pruttelherrie/Ehx9-All/controller-firmware/include/Amiga4Ever6pt7b.h

const uint8_t amiga4ever6pt7bBitmaps[] PROGMEM = {
  0x00, 0xFF, 0xFF, 0xFF, 0x00, 0x0F, 0xF0, 0xF7, 0xF7, 0xF7, 0xF0, 0x7B,
  0x8F, 0x71, 0xEE, 0x7F, 0xFF, 0xFE, 0xF7, 0x3F, 0xFF, 0xFF, 0x7B, 0x8F,
  0x71, 0xEE, 0x00, 0x1E, 0x0F, 0xF3, 0xFF, 0xC0, 0xF0, 0x0F, 0xC3, 0xF0,
  0x0F, 0xFF, 0x3F, 0xC1, 0xE0, 0x38, 0xE7, 0x1F, 0x6E, 0x73, 0x81, 0x6E,
  0x39, 0xCE, 0xDF, 0x1C, 0xE3, 0x80, 0x1F, 0x00, 0xF8, 0x0E, 0xF0, 0x77,
  0x83, 0xB0, 0x1E, 0x70, 0xF3, 0x9D, 0xF8, 0xE3, 0xE1, 0xFF, 0xCF, 0xFE,
  0x7B, 0xDF, 0xCE, 0x00, 0x1C, 0x77, 0xB8, 0xE3, 0x8E, 0x38, 0x78, 0x71,
  0xC0, 0xE3, 0x87, 0x87, 0x1C, 0x71, 0xC7, 0x7B, 0x8E, 0x00, 0x79, 0xE7,
  0x9E, 0x1F, 0x8F, 0xFF, 0xFF, 0xF1, 0xF8, 0x79, 0xE7, 0x9E, 0x1E, 0x07,
  0x81, 0xE3, 0xFF, 0xFF, 0xC7, 0x81, 0xE0, 0x7B, 0xDF, 0xC0, 0xFF, 0xFF,
  0xF0, 0xFF, 0xF0, 0x00, 0x70, 0x07, 0x01, 0xE0, 0x38, 0x03, 0x80, 0xF0,
  0x1C, 0x01, 0xC0, 0x78, 0x0E, 0x00, 0xE0, 0x00, 0x3F, 0x0F, 0xCF, 0x3F,
  0xDF, 0xF7, 0xFF, 0xFF, 0xBF, 0xEF, 0xF3, 0xCF, 0xC3, 0xF0, 0x1E, 0x7C,
  0xFF, 0xFF, 0xE3, 0xC7, 0x8F, 0x1E, 0x3C, 0x78, 0x3F, 0x0F, 0xCF, 0x3F,
  0xCF, 0x03, 0xC1, 0xC1, 0xE0, 0x78, 0x38, 0x3F, 0xFF, 0xFC, 0x3F, 0x0F,
  0xCF, 0x3F, 0xCF, 0x03, 0xC7, 0xC1, 0xF0, 0x0F, 0xF3, 0xFC, 0xF3, 0xF0,
  0x0F, 0x81, 0xF0, 0x7E, 0x3D, 0xC7, 0xB9, 0xC7, 0x3F, 0xFF, 0xFF, 0x03,
  0x80, 0x70, 0x0E, 0x00, 0xFF, 0xFF, 0xFF, 0x03, 0xFC, 0xFF, 0x00, 0xF0,
  0x3C, 0x0F, 0xF3, 0xFC, 0xF3, 0xF0, 0x1F, 0x07, 0xC3, 0x83, 0xE0, 0xF0,
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
  {   418,  10,  11,  12,    1,  -10 },   // 0x46 'F'
  {   432,  10,  11,  12,    1,  -10 },   // 0x47 'G'
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

const GFXfont amiga4ever6pt7b PROGMEM = {
  (uint8_t  *)amiga4ever6pt7bBitmaps,
  (GFXglyph *)amiga4ever6pt7bGlyphs,
  0x20, 0x7E, 12 };

// Approx. 1783 bytes
