pruttelherrie/Ehx9-All/controller-firmware/include/Amiga4Ever8pt7b.h

const uint8_t amiga4ever8pt7bBitmaps[] PROGMEM = {
  0x00, 0xFF, 0xFF, 0xFF, 0xFF, 0x00, 0x00, 0xFF, 0xF3, 0xFC, 0xFF, 0x3F,
  0xCF, 0x3C, 0xF0, 0xF3, 0xC3, 0xCF, 0x0F, 0x3C, 0xFF, 0xFF, 0xFF, 0xF3,
  0xCF, 0x0F, 0x3C, 0xFF, 0xFF, 0xFF, 0xF3, 0xCF, 0x0F, 0x3C, 0x3C, 0xF0,
  0xF3, 0xC0, 0x0F, 0x00, 0xF0, 0x3F, 0xF3, 0xFF, 0xF0, 0x0F, 0x00, 0x3F,
  0xC3, 0xFC, 0x00, 0xF0, 0x0F, 0xFF, 0xCF, 0xFC, 0x0F, 0x00, 0xF0, 0x3C,
  0x3C, 0xF0, 0xFC, 0xCF, 0x33, 0x3C, 0xF3, 0xC3, 0xCF, 0x00, 0xF3, 0xC3,
  0xCF, 0x3C, 0xCC, 0xF3, 0x3F, 0x0F, 0x3C, 0x3C, 0x0F, 0xC0, 0x0F, 0xC0,
  0x3C, 0xF0, 0x3C, 0xF0, 0x3C, 0xC0, 0x3C, 0xC0, 0x3F, 0x3C, 0x3F, 0x3C,
  0xF3, 0xF0, 0xF3, 0xF0, 0xF0, 0xFC, 0xF0, 0xFC, 0x3F, 0xFF, 0x3F, 0xFF,
  0x3C, 0xF3, 0xCF, 0xF3, 0xC0, 0x0F, 0x0F, 0x3C, 0x3C, 0xF0, 0xF0, 0xF0,
  0xF0, 0xF0, 0xF0, 0x3C, 0x3C, 0x0F, 0x0F, 0xF0, 0xF0, 0x3C, 0x3C, 0x0F,
  0x0F, 0x0F, 0x0F, 0x0F, 0x0F, 0x3C, 0x3C, 0xF0, 0xF0, 0x3C, 0x3C, 0x3C,
  0x3C, 0x0F, 0xF0, 0x0F, 0xF0, 0xFF, 0xFF, 0xFF, 0xFF, 0x0F, 0xF0, 0x0F,
  0xF0, 0x3C, 0x3C, 0x3C, 0x3C, 0x0F, 0x00, 0xF0, 0x0F, 0x00, 0xF0, 0xFF,
  0xFF, 0xFF, 0x0F, 0x00, 0xF0, 0x0F, 0x00, 0xF0, 0x3C, 0xF3, 0xCF, 0xF3,
  0xC0, 0xFF, 0xFF, 0xFF, 0xFF, 0xFF, 0x00, 0x0F, 0x00, 0x0F, 0x00, 0x3C,
  0x00, 0x3C, 0x00, 0xF0, 0x00, 0xF0, 0x03, 0xC0, 0x03, 0xC0, 0x0F, 0x00,
  0x0F, 0x00, 0x3C, 0x00, 0x3C, 0x00, 0xF0, 0x00, 0xF0, 0x00, 0x3F, 0xC3,
  0xFC, 0xF0, 0xFF, 0x0F, 0xF3, 0xFF, 0x3F, 0xFF, 0xFF, 0xFF, 0xFC, 0xFF,
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
  {   628,  12,  14,  16,    2,  -13 },   // 0x46 'F'
  {   649,  12,  14,  16,    2,  -13 },   // 0x47 'G'
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

const GFXfont amiga4ever8pt7b PROGMEM = {
  (uint8_t  *)amiga4ever8pt7bBitmaps,
  (GFXglyph *)amiga4ever8pt7bGlyphs,
  0x20, 0x7E, 16 };

// Approx. 2344 bytes
