pruttelherrie/Ehx9-All/controller-firmware/include/LiberationSans8pt7b.h

const uint8_t LiberationSans_Regular8pt7bBitmaps[] PROGMEM = {
  0x00, 0xFF, 0x60, 0x99, 0x90, 0x11, 0x08, 0x84, 0x5F, 0xF2, 0x21, 0x10,
  0x89, 0xFF, 0x44, 0x22, 0x11, 0x00, 0x10, 0xFA, 0x4C, 0x89, 0x0A, 0x0E,
  0x0A, 0x12, 0x26, 0x4B, 0xE1, 0x00, 0x70, 0x48, 0x88, 0x88, 0x88, 0x90,
  0x8A, 0x07, 0x4E, 0x05, 0x10, 0x91, 0x11, 0x11, 0x11, 0x20, 0xE0, 0x1C,
  0x11, 0x08, 0x84, 0x82, 0x82, 0x8A, 0x25, 0x12, 0x86, 0x43, 0x1E, 0x60,
  0xE0, 0x12, 0x44, 0x88, 0x88, 0x88, 0x84, 0x42, 0x10, 0x84, 0x22, 0x11,
  0x11, 0x11, 0x12, 0x24, 0x80, 0x21, 0x3E, 0x45, 0x44, 0x10, 0x20, 0x47,
  0xF1, 0x02, 0x04, 0x00, 0x56, 0xE0, 0xC0, 0x11, 0x22, 0x22, 0x44, 0x44,
  0x88, 0x38, 0x8A, 0x0C, 0x18, 0x30, 0x60, 0xC1, 0x82, 0x88, 0xE0, 0x30,
  0xA2, 0x40, 0x81, 0x02, 0x04, 0x08, 0x10, 0x23, 0xF8, 0x79, 0x08, 0x08,
  0x10, 0x20, 0x82, 0x18, 0x41, 0x03, 0xF8, 0x79, 0x08, 0x08, 0x10, 0x43,
  0x01, 0x01, 0x03, 0x09, 0xE0, 0x04, 0x0C, 0x14, 0x24, 0x24, 0x44, 0x84,
  0xFF, 0x04, 0x04, 0x04, 0xFF, 0x02, 0x04, 0x0B, 0x98, 0x80, 0x81, 0x03,
  0x09, 0xE0, 0x3C, 0x86, 0x04, 0x0B, 0x98, 0xA0, 0xC1, 0x82, 0x88, 0xE0,
  0xFE, 0x04, 0x10, 0x40, 0x82, 0x04, 0x08, 0x20, 0x40, 0x80, 0x38, 0x8A,
  0x0C, 0x14, 0x47, 0x11, 0x41, 0x82, 0x88, 0xE0, 0x38, 0x8A, 0x0C, 0x18,
  0x28, 0xCE, 0x81, 0x03, 0x09, 0xE0, 0xC1, 0x80, 0x50, 0x01, 0x58, 0x02,
  0x39, 0x84, 0x06, 0x03, 0x80, 0x80, 0xFE, 0x00, 0x00, 0x0F, 0xE0, 0x80,
  0xE0, 0x30, 0x10, 0xCE, 0x20, 0x00, 0x38, 0x8A, 0x08, 0x10, 0x20, 0x82,
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
  {   338,  10,  11,  12,    1,  -10 },   // 0x47 'G'
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

const GFXfont LiberationSans_Regular8pt7b PROGMEM = {
  (uint8_t  *)LiberationSans_Regular8pt7bBitmaps,
  (GFXglyph *)LiberationSans_Regular8pt7bGlyphs,
  0x20, 0x7E, 18 };

// Approx. 1539 bytes
