pruttelherrie/Ehx9-All/controller-firmware/include/LiberationSansBold7pt7b.h

const uint8_t LiberationSans_Bold7pt7bBitmaps[] PROGMEM = {
  0x00, 0xFF, 0xFC, 0xF0, 0xDE, 0xF7, 0xB0, 0x12, 0x12, 0x12, 0x7F, 0x24,
  0x24, 0xFE, 0x48, 0x48, 0x48, 0x11, 0xEF, 0xFB, 0xE1, 0xE0, 0xF3, 0xFD,
  0xE1, 0x00, 0x61, 0x24, 0x89, 0x22, 0x50, 0x95, 0x9A, 0x90, 0xA4, 0x49,
  0x12, 0x48, 0x60, 0x38, 0x7C, 0x6C, 0x78, 0x63, 0xF3, 0xDE, 0xCC, 0xFF,
  0x73, 0xFF, 0x36, 0x6C, 0xCC, 0xCC, 0xCC, 0xC6, 0x63, 0xC6, 0x63, 0x33,
  0x33, 0x33, 0x36, 0x6C, 0x25, 0x7E, 0xA5, 0x00, 0x18, 0x18, 0x18, 0xFF,
  0xFF, 0x18, 0x18, 0x18, 0xF7, 0xFC, 0xF0, 0x33, 0x32, 0x66, 0x64, 0xCC,
  0xC0, 0x79, 0xEC, 0xF3, 0xCF, 0x3C, 0xF3, 0x79, 0xE0, 0x73, 0xCB, 0x0C,
  0x30, 0xC3, 0x0C, 0xFF, 0xF0, 0x7B, 0xFC, 0xC3, 0x1C, 0xE7, 0x18, 0xFF,
  0xF0, 0x7B, 0xFC, 0xC3, 0x38, 0xE0, 0xF3, 0xFD, 0xE0, 0x1C, 0x38, 0xF1,
  0x64, 0xD9, 0xBF, 0xFF, 0x0C, 0x18, 0xFF, 0xFC, 0x3E, 0xFC, 0x30, 0xF3,
  0xFD, 0xE0, 0x39, 0xFC, 0xF0, 0xFB, 0xFC, 0xF3, 0x7D, 0xE0, 0xFF, 0xF0,
  0xC6, 0x18, 0xC3, 0x18, 0x61, 0x80, 0x7B, 0xFC, 0xF3, 0x79, 0xEC, 0xF3,
  0xFD, 0xE0, 0x7B, 0xEC, 0xF3, 0xFD, 0xF0, 0xF3, 0xF9, 0xC0, 0xF0, 0x0F,
  0xF0, 0x0F, 0x70, 0x04, 0xFF, 0xB8, 0xE3, 0xE3, 0xC1, 0xFF, 0xF0, 0x3F,
  0xFC, 0x83, 0xC7, 0xC7, 0x1D, 0xFF, 0x20, 0x3D, 0xFF, 0x18, 0x30, 0xC3,
  0x0C, 0x00, 0x30, 0x60, 0x0F, 0x83, 0x06, 0x60, 0x24, 0xE9, 0x89, 0x99,
  0x11, 0x91, 0x19, 0x32, 0x8D, 0xC4, 0x00, 0x60, 0xC1, 0xF8, 0x1C, 0x0E,
  0x0D, 0x86, 0xC3, 0x63, 0x19, 0xFC, 0xFE, 0xE1, 0xE0, 0xC0, 0xFE, 0xFF,
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
  {   265,   7,  10,   9,    1,   -9 },   // 0x46 'F'
  {   274,   9,  10,  11,    1,   -9 },   // 0x47 'G'
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

const GFXfont LiberationSans_Bold7pt7b PROGMEM = {
  (uint8_t  *)LiberationSans_Bold7pt7bBitmaps,
  (GFXglyph *)LiberationSans_Bold7pt7bGlyphs,
  0x20, 0x7E, 16 };

// Approx. 1410 bytes
