pruttelherrie/Ehx9-All/controller-firmware/include/lovecraft24pt7b.h

const uint8_t Love_Craft_Italic24pt7bBitmaps[] PROGMEM = {
  0x00, 0x00, 0x03, 0xFF, 0x80, 0x00, 0x00, 0x00, 0xFF, 0xFF, 0x80, 0x00,
  0x00, 0x3F, 0xFF, 0xFF, 0x00, 0x00, 0x03, 0xFF, 0xFF, 0xFE, 0x00, 0x00,
  0x7F, 0xFC, 0x7F, 0xF8, 0x00, 0x0F, 0xFF, 0x81, 0xFF, 0xE0, 0x00, 0xFF,
  0xF8, 0x0F, 0xFF, 0x00, 0x0F, 0xFF, 0x80, 0x3F, 0xFC, 0x00, 0xFF, 0xF8,
  0x01, 0xFF, 0xE0, 0x0F, 0xFF, 0xC0, 0x0F, 0xFF, 0x80, 0xFF, 0xFC, 0x00,
  0x7F, 0xFC, 0x07, 0xFF, 0xE0, 0x03, 0xFF, 0xE0, 0x7F, 0xFE, 0x00, 0x1F,
  0xFF, 0x07, 0xFF, 0xF0, 0x00, 0xFF, 0xF8, 0x3F, 0xFF, 0x00, 0x07, 0xFF,
  0xE3, 0xFF, 0xF8, 0x00, 0x3F, 0xFF, 0x1F, 0xFF, 0xC0, 0x01, 0xFF, 0xF8,
  0xFF, 0xFC, 0x00, 0x1F, 0xFF, 0x87, 0xFF, 0xE0, 0x00, 0xFF, 0xFC, 0x7F,
  0xFF, 0x00, 0x07, 0xFF, 0xE3, 0xFF, 0xF0, 0x00, 0x3F, 0xFF, 0x1F, 0xFF,
  0x80, 0x03, 0xFF, 0xF0, 0xFF, 0xFC, 0x00, 0x1F, 0xFF, 0x87, 0xFF, 0xE0,
  0x01, 0xFF, 0xFC, 0x3F, 0xFF, 0x00, 0x0F, 0xFF, 0xC1, 0xFF, 0xF8, 0x00,
  0x7F, 0xFC, 0x0F, 0xFF, 0xC0, 0x07, 0xFF, 0xE0, 0x3F, 0xFE, 0x00, 0x3F,
  0xFE, 0x01, 0xFF, 0xF0, 0x03, 0xFF, 0xE0, 0x0F, 0xFF, 0x80, 0x3F, 0xFE,
  0x00, 0x3F, 0xFC, 0x01, 0xFF, 0xF0, 0x01, 0xFF, 0xE0, 0x1F, 0xFE, 0x00,
  0x07, 0xFF, 0x81, 0xFF, 0xE0, 0x00, 0x1F, 0xFE, 0x3F, 0xFE, 0x00, 0x00,
  0x7F, 0xFF, 0xFF, 0xE0, 0x00, 0x00, 0xFF, 0xFF, 0xFC, 0x00, 0x00, 0x01,
  0xFF, 0xFF, 0x00, 0x00, 0x00, 0x01, 0xFF, 0xC0, 0x00, 0x00, 0x00, 0x00,
  0x03, 0x80, 0x00, 0x07, 0xC0, 0x00, 0x3F, 0xE0, 0x00, 0xFF, 0xF0, 0x07,
  0xFF, 0xF8, 0x1F, 0xFF, 0xF8, 0x0F, 0xFF, 0xFC, 0x01, 0xFF, 0xFE, 0x00,
  0x3F, 0xFF, 0x00, 0x0F, 0xFF, 0x80, 0x0F, 0xFF, 0x80, 0x07, 0xFF, 0xC0,
  0x03, 0xFF, 0xE0, 0x01, 0xFF, 0xF0, 0x00, 0xFF, 0xF8, 0x00, 0xFF, 0xF8,
  0x00, 0x7F, 0xFC, 0x00, 0x3F, 0xFE, 0x00, 0x1F, 0xFF, 0x00, 0x1F, 0xFF,
  0x80, 0x0F, 0xFF, 0x80, 0x07, 0xFF, 0xC0, 0x03, 0xFF, 0xE0, 0x01, 0xFF,
  0xF0, 0x01, 0xFF, 0xF8, 0x00, 0xFF, 0xF8, 0x00, 0x7F, 0xFC, 0x00, 0x3F,
  0xFE, 0x00, 0x1F, 0xFF, 0x00, 0x1F, 0xFF, 0x80, 0x0F, 0xFF, 0x80, 0x07,
  0xFF, 0xC0, 0x03, 0xFF, 0xE0, 0x03, 0xFF, 0xF0, 0x03, 0xFF, 0xF8, 0x07,
  0xFF, 0xFE, 0x0F, 0xFF, 0xFF, 0xE7, 0xFF, 0xFF, 0xE0, 0x00, 0x00, 0x0F,
  0xFF, 0xC0, 0x00, 0x00, 0x1F, 0xFF, 0xFF, 0xC0, 0x00, 0x0F, 0xFF, 0xFF,
  0xFF, 0x00, 0x03, 0xFF, 0xFF, 0xFF, 0xF8, 0x00, 0xFF, 0xF8, 0x1F, 0xFF,
  0xC0, 0x1F, 0xFE, 0x00, 0x7F, 0xFE, 0x03, 0xFF, 0xC0, 0x03, 0xFF, 0xE0,
  0x3F, 0xF8, 0x00, 0x3F, 0xFF, 0x07, 0xFF, 0x80, 0x01, 0xFF, 0xF0, 0x7F,
  0xF8, 0x00, 0x1F, 0xFF, 0x03, 0xFF, 0x80, 0x01, 0xFF, 0xF0, 0x3F, 0xFF,
  0x80, 0x3F, 0xFF, 0x01, 0xFF, 0xF8, 0x03, 0xFF, 0xF0, 0x0F, 0xFF, 0x00,
  0x7F, 0xFE, 0x00, 0x7F, 0xF0, 0x0F, 0xFF, 0xE0, 0x01, 0xFC, 0x01, 0xFF,
  0xFC, 0x00, 0x00, 0x00, 0x3F, 0xFF, 0x80, 0x00, 0x00, 0x0F, 0xFF, 0xF0,
  0x00, 0x00, 0x01, 0xFF, 0xFE, 0x00, 0x00, 0x00, 0x7F, 0xFF, 0x80, 0x00,
  0x00, 0x1F, 0xFF, 0xF0, 0x00, 0x00, 0x07, 0xFF, 0xFC, 0x00, 0x00, 0x01,
  0xFF, 0xFF, 0x00, 0x00, 0x00, 0x7F, 0xFF, 0xC0, 0x00, 0x00, 0x0F, 0xFF,
  0xF0, 0x00, 0x00, 0x03, 0xFF, 0xF8, 0x00, 0x00, 0x00, 0x7F, 0xFC, 0x00,
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

const GFXglyph Love_Craft_Italic24pt7bGlyphs[] PROGMEM = {
  {     0,  45,  38,  43,    1,  -34 },   // 0x30 '0'
  {   214,  25,  38,  31,    5,  -34 },   // 0x31 '1'
  {   333,  44,  38,  42,    2,  -34 },   // 0x32 '2'
  {   542,  42,  38,  40,    2,  -34 },   // 0x33 '3'
  {   742,  43,  38,  44,    2,  -34 },   // 0x34 '4'
  {   947,  40,  38,  39,    2,  -34 },   // 0x35 '5'
  {  1137,  40,  38,  38,    3,  -34 },   // 0x36 '6'
  {  1327,  40,  39,  41,    7,  -35 },   // 0x37 '7'
  {  1522,  39,  38,  39,    3,  -34 },   // 0x38 '8'
  {  1708,  39,  38,  38,    3,  -34 } }; // 0x39 '9'

const GFXfont Love_Craft_Italic24pt7b PROGMEM = {
  (uint8_t  *)Love_Craft_Italic24pt7bBitmaps,
  (GFXglyph *)Love_Craft_Italic24pt7bGlyphs,
  0x30, 0x39, 65 };

// Approx. 1971 bytes
