pruttelherrie/Ehx9-All/controller-firmware/include/lovecraft30pt7b.h

const uint8_t Love_Craft_Italic30pt7bBitmaps[] PROGMEM = {
  0x00, 0x00, 0x00, 0x07, 0xFF, 0x80, 0x00, 0x00, 0x00, 0x00, 0x7F, 0xFF,
  0xF8, 0x00, 0x00, 0x00, 0x03, 0xFF, 0xFF, 0xFE, 0x00, 0x00, 0x00, 0x0F,
  0xFF, 0xFF, 0xFF, 0x80, 0x00, 0x00, 0x3F, 0xFF, 0xFF, 0xFF, 0xC0, 0x00,
  0x00, 0xFF, 0xFF, 0x87, 0xFF, 0xE0, 0x00, 0x01, 0xFF, 0xFE, 0x03, 0xFF,
  0xF0, 0x00, 0x03, 0xFF, 0xFC, 0x03, 0xFF, 0xF8, 0x00, 0x0F, 0xFF, 0xF8,
  0x03, 0xFF, 0xFC, 0x00, 0x1F, 0xFF, 0xF0, 0x01, 0xFF, 0xFC, 0x00, 0x3F,
  0xFF, 0xE0, 0x01, 0xFF, 0xFE, 0x00, 0x7F, 0xFF, 0xC0, 0x01, 0xFF, 0xFE,
  0x00, 0x7F, 0xFF, 0xC0, 0x01, 0xFF, 0xFE, 0x00, 0xFF, 0xFF, 0x80, 0x01,
  0xFF, 0xFE, 0x01, 0xFF, 0xFF, 0x80, 0x01, 0xFF, 0xFF, 0x03, 0xFF, 0xFF,
  0x00, 0x01, 0xFF, 0xFF, 0x03, 0xFF, 0xFF, 0x00, 0x01, 0xFF, 0xFF, 0x07,
  0xFF, 0xFE, 0x00, 0x01, 0xFF, 0xFF, 0x07, 0xFF, 0xFE, 0x00, 0x01, 0xFF,
  0xFF, 0x0F, 0xFF, 0xFE, 0x00, 0x01, 0xFF, 0xFF, 0x0F, 0xFF, 0xFC, 0x00,
  0x03, 0xFF, 0xFF, 0x0F, 0xFF, 0xFC, 0x00, 0x03, 0xFF, 0xFF, 0x0F, 0xFF,
  0xFC, 0x00, 0x03, 0xFF, 0xFF, 0x1F, 0xFF, 0xF8, 0x00, 0x03, 0xFF, 0xFE,
  0x1F, 0xFF, 0xF8, 0x00, 0x07, 0xFF, 0xFE, 0x1F, 0xFF, 0xF8, 0x00, 0x07,
  0xFF, 0xFE, 0x1F, 0xFF, 0xF0, 0x00, 0x07, 0xFF, 0xFE, 0x1F, 0xFF, 0xF0,
  0x00, 0x0F, 0xFF, 0xFC, 0x1F, 0xFF, 0xF0, 0x00, 0x0F, 0xFF, 0xFC, 0x1F,
  0xFF, 0xF0, 0x00, 0x0F, 0xFF, 0xF8, 0x1F, 0xFF, 0xF0, 0x00, 0x1F, 0xFF,
  0xF8, 0x1F, 0xFF, 0xF0, 0x00, 0x1F, 0xFF, 0xF0, 0x1F, 0xFF, 0xF0, 0x00,
  0x3F, 0xFF, 0xE0, 0x1F, 0xFF, 0xF0, 0x00, 0x3F, 0xFF, 0xE0, 0x0F, 0xFF,
  0xF0, 0x00, 0x7F, 0xFF, 0xC0, 0x0F, 0xFF, 0xF0, 0x00, 0x7F, 0xFF, 0x80,
  0x0F, 0xFF, 0xF0, 0x00, 0xFF, 0xFF, 0x00, 0x07, 0xFF, 0xF0, 0x01, 0xFF,
  0xFE, 0x00, 0x07, 0xFF, 0xF0, 0x01, 0xFF, 0xFC, 0x00, 0x03, 0xFF, 0xF8,
  0x03, 0xFF, 0xF8, 0x00, 0x01, 0xFF, 0xF8, 0x0F, 0xFF, 0xF0, 0x00, 0x00,
  0xFF, 0xFE, 0x3F, 0xFF, 0xE0, 0x00, 0x00, 0x7F, 0xFF, 0xFF, 0xFF, 0xC0,
  0x00, 0x00, 0x3F, 0xFF, 0xFF, 0xFF, 0x00, 0x00, 0x00, 0x0F, 0xFF, 0xFF,
  0xF8, 0x00, 0x00, 0x00, 0x01, 0xFF, 0xFF, 0xE0, 0x00, 0x00, 0x00, 0x00,
  0x1F, 0xFC, 0x00, 0x00, 0x00, 0x00, 0x00, 0x00, 0x0E, 0x00, 0x00, 0x00,
  0x7F, 0x00, 0x00, 0x03, 0xFF, 0x00, 0x00, 0x1F, 0xFE, 0x00, 0x01, 0xFF,
  0xFE, 0x00, 0x1F, 0xFF, 0xFE, 0x00, 0xFF, 0xFF, 0xFE, 0x00, 0xFF, 0xFF,
  0xFE, 0x00, 0x7F, 0xFF, 0xFC, 0x00, 0x0F, 0xFF, 0xFC, 0x00, 0x07, 0xFF,
  0xFC, 0x00, 0x07, 0xFF, 0xFC, 0x00, 0x07, 0xFF, 0xFC, 0x00, 0x07, 0xFF,
  0xF8, 0x00, 0x07, 0xFF, 0xF8, 0x00, 0x07, 0xFF, 0xF8, 0x00, 0x0F, 0xFF,
  0xF8, 0x00, 0x0F, 0xFF, 0xF0, 0x00, 0x0F, 0xFF, 0xF0, 0x00, 0x0F, 0xFF,
  0xF0, 0x00, 0x0F, 0xFF, 0xF0, 0x00, 0x1F, 0xFF, 0xF0, 0x00, 0x1F, 0xFF,
  0xE0, 0x00, 0x1F, 0xFF, 0xE0, 0x00, 0x1F, 0xFF, 0xE0, 0x00, 0x3F, 0xFF,
  0xE0, 0x00, 0x3F, 0xFF, 0xE0, 0x00, 0x3F, 0xFF, 0xC0, 0x00, 0x3F, 0xFF,
  0xC0, 0x00, 0x3F, 0xFF, 0xC0, 0x00, 0x7F, 0xFF, 0xC0, 0x00, 0x7F, 0xFF,
  0x80, 0x00, 0x7F, 0xFF, 0x80, 0x00, 0x7F, 0xFF, 0x80, 0x00, 0x7F, 0xFF,
  0x80, 0x00, 0xFF, 0xFF, 0x80, 0x00, 0xFF, 0xFF, 0x00, 0x00, 0xFF, 0xFF,
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

const GFXglyph Love_Craft_Italic30pt7bGlyphs[] PROGMEM = {
  {     0,  56,  47,  54,    1,  -42 },   // 0x30 '0'
  {   329,  32,  46,  39,    6,  -42 },   // 0x31 '1'
  {   513,  56,  47,  53,    2,  -43 },   // 0x32 '2'
  {   842,  52,  46,  50,    2,  -42 },   // 0x33 '3'
  {  1141,  54,  46,  55,    2,  -42 },   // 0x34 '4'
  {  1452,  51,  47,  49,    2,  -42 },   // 0x35 '5'
  {  1752,  50,  47,  47,    4,  -42 },   // 0x36 '6'
  {  2046,  51,  48,  51,    8,  -43 },   // 0x37 '7'
  {  2352,  48,  47,  49,    4,  -42 },   // 0x38 '8'
  {  2634,  48,  47,  48,    4,  -42 } }; // 0x39 '9'

const GFXfont Love_Craft_Italic30pt7b PROGMEM = {
  (uint8_t  *)Love_Craft_Italic30pt7bBitmaps,
  (GFXglyph *)Love_Craft_Italic30pt7bGlyphs,
  0x30, 0x39, 81 };

// Approx. 2993 bytes
