pruttelherrie/Ehx9-All/controller-firmware/include/lovecraft72pt7b.h

const uint8_t Love_Craft_Italic48pt7bBitmaps[] PROGMEM = {
  0x00, 0x3F, 0xFF, 0xFF, 0xFF, 0xFF, 0xC0, 0x0F, 0xFF, 0xFF, 0xFF, 0xFF,
  0xF0, 0x03, 0xFF, 0xFF, 0xFF, 0xFF, 0xFC, 0x00, 0xE0, 0x00, 0x00, 0x00,
  0x0F, 0x00, 0x78, 0x00, 0x00, 0x00, 0x03, 0x80, 0x1E, 0x00, 0x00, 0x00,
  0x00, 0xE0, 0x07, 0x00, 0x00, 0x00, 0x00, 0x78, 0x01, 0xC0, 0x00, 0x00,
  0x00, 0x1E, 0x00, 0x70, 0x00, 0x00, 0x00, 0x07, 0x00, 0x3C, 0x00, 0x00,
  0x00, 0x01, 0xC0, 0x0F, 0x00, 0x00, 0x00, 0x00, 0x70, 0x03, 0x80, 0x00,
  0x00, 0x00, 0x3C, 0x00, 0xE0, 0x00, 0x00, 0x00, 0x0F, 0x00, 0x78, 0x00,
  0x00, 0x00, 0x03, 0x80, 0x1E, 0x00, 0x00, 0x00, 0x00, 0xE0, 0x07, 0x80,
  0x00, 0x00, 0x00, 0x78, 0x01, 0xC0, 0x00, 0x00, 0x00, 0x1E, 0x00, 0x70,
  0x00, 0x00, 0x00, 0x07, 0x00, 0x3C, 0x00, 0x00, 0x00, 0x01, 0xC0, 0x0F,
  0x00, 0x00, 0x00, 0x00, 0x70, 0x03, 0x80, 0x00, 0x00, 0x00, 0x3C, 0x00,
  0xE0, 0x00, 0x00, 0x00, 0x0F, 0x00, 0x78, 0x00, 0x00, 0x00, 0x03, 0x80,
  0x1E, 0x00, 0x00, 0x00, 0x00, 0xE0, 0x07, 0x80, 0x00, 0x00, 0x00, 0x78,
  0x01, 0xC0, 0x00, 0x00, 0x00, 0x1E, 0x00, 0x70, 0x00, 0x00, 0x00, 0x07,
  0x80, 0x3C, 0x00, 0x00, 0x00, 0x01, 0xC0, 0x0F, 0x00, 0x00, 0x00, 0x00,
  0x70, 0x03, 0x80, 0x00, 0x00, 0x00, 0x3C, 0x00, 0xE0, 0x00, 0x00, 0x00,
  0x0F, 0x00, 0x38, 0x00, 0x00, 0x00, 0x03, 0x80, 0x1E, 0x00, 0x00, 0x00,
  0x00, 0xE0, 0x07, 0x80, 0x00, 0x00, 0x00, 0x38, 0x01, 0xC0, 0x00, 0x00,
  0x00, 0x1E, 0x00, 0x70, 0x00, 0x00, 0x00, 0x07, 0x80, 0x3C, 0x00, 0x00,
  0x00, 0x01, 0xC0, 0x0F, 0x00, 0x00, 0x00, 0x00, 0x70, 0x03, 0xC0, 0x00,
  0x00, 0x00, 0x3C, 0x00, 0xE0, 0x00, 0x00, 0x00, 0x0F, 0x00, 0x38, 0x00,
  0x00, 0x00, 0x03, 0xC0, 0x1E, 0x00, 0x00, 0x00, 0x00, 0xE0, 0x07, 0x80,
  0x00, 0x00, 0x00, 0x38, 0x01, 0xC0, 0x00, 0x00, 0x00, 0x1E, 0x00, 0x70,
  0x00, 0x00, 0x00, 0x07, 0x80, 0x1F, 0xFF, 0xFF, 0xFF, 0xFF, 0xC0, 0x0F,
  0xFF, 0xFF, 0xFF, 0xFF, 0xF0, 0x03, 0xFF, 0xFF, 0xFF, 0xFF, 0xFC, 0x00,
  0x00, 0x3F, 0xFF, 0xFF, 0xFF, 0xFF, 0xC0, 0x0F, 0xFF, 0xFF, 0xFF, 0xFF,
  0xF0, 0x03, 0xFF, 0xFF, 0xFF, 0xFF, 0xFC, 0x00, 0xE0, 0x00, 0x00, 0x00,
  0x0F, 0x00, 0x78, 0x00, 0x00, 0x00, 0x03, 0x80, 0x1E, 0x00, 0x00, 0x00,
  0x00, 0xE0, 0x07, 0x00, 0x00, 0x00, 0x00, 0x78, 0x01, 0xC0, 0x00, 0x00,
  0x00, 0x1E, 0x00, 0x70, 0x00, 0x00, 0x00, 0x07, 0x00, 0x3C, 0x00, 0x00,
  0x00, 0x01, 0xC0, 0x0F, 0x00, 0x00, 0x00, 0x00, 0x70, 0x03, 0x80, 0x00,
  0x00, 0x00, 0x3C, 0x00, 0xE0, 0x00, 0x00, 0x00, 0x0F, 0x00, 0x78, 0x00,
  0x00, 0x00, 0x03, 0x80, 0x1E, 0x00, 0x00, 0x00, 0x00, 0xE0, 0x07, 0x80,
  0x00, 0x00, 0x00, 0x78, 0x01, 0xC0, 0x00, 0x00, 0x00, 0x1E, 0x00, 0x70,
  0x00, 0x00, 0x00, 0x07, 0x00, 0x3C, 0x00, 0x00, 0x00, 0x01, 0xC0, 0x0F,
  0x00, 0x00, 0x00, 0x00, 0x70, 0x03, 0x80, 0x00, 0x00, 0x00, 0x3C, 0x00,
  0xE0, 0x00, 0x00, 0x00, 0x0F, 0x00, 0x78, 0x00, 0x00, 0x00, 0x03, 0x80,
  0x1E, 0x00, 0x00, 0x00, 0x00, 0xE0, 0x07, 0x80, 0x00, 0x00, 0x00, 0x78,
  0x01, 0xC0, 0x00, 0x00, 0x00, 0x1E, 0x00, 0x70, 0x00, 0x00, 0x00, 0x07,
  0x80, 0x3C, 0x00, 0x00, 0x00, 0x01, 0xC0, 0x0F, 0x00, 0x00, 0x00, 0x00,
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

const GFXglyph Love_Craft_Italic48pt7bGlyphs[] PROGMEM = {
  {     0,  50,  48,  42,    3,  -56 },   // 0x10
  {   300,  50,  48,  42,    3,  -56 },   // 0x11
  {   600,  50,  48,  42,    3,  -56 },   // 0x12
  {   900,  50,  48,  42,    3,  -56 },   // 0x13
  {  1200,  50,  48,  42,    3,  -56 },   // 0x14
  {  1500,  50,  48,  42,    3,  -56 },   // 0x15
  {  1800,  50,  48,  42,    3,  -56 },   // 0x16
  {  2100,  50,  48,  42,    3,  -56 },   // 0x17
  {  2400,  50,  48,  42,    3,  -56 },   // 0x18
  {  2700,  50,  48,  42,    3,  -56 } }; // 0x19

const GFXfont Love_Craft_Italic48pt7b PROGMEM = {
  (uint8_t  *)Love_Craft_Italic48pt7bBitmaps,
  (GFXglyph *)Love_Craft_Italic48pt7bGlyphs,
  0x10, 0x19, 130 };

// Approx. 3077 bytes
