pruttelherrie/Ehx9-All/controller-firmware/include/neon64.h

const uint8_t Neon64pt7bBitmaps[] PROGMEM = {
  0x00, 0x00, 0x00, 0x00, 0x00, 0x00, 0x00, 0x00, 0x00, 0x00, 0x00, 0x00,
  0x00, 0x00, 0x00, 0x00, 0x00, 0x00, 0x00, 0x00, 0x00, 0x00, 0x00, 0x00,
  0x00, 0x00, 0x00, 0x00, 0x00, 0x00, 0x00, 0x00, 0x00, 0x00, 0x00, 0x01,
  0xFF, 0xC0, 0x00, 0x00, 0x00, 0x00, 0x0F, 0xFF, 0xFE, 0x00, 0x00, 0x00,
  0x00, 0x1F, 0x00, 0x0F, 0xC0, 0x00, 0x00, 0x00, 0x3C, 0x00, 0x00, 0xF8,
  0x00, 0x00, 0x00, 0x78, 0x0F, 0xFC, 0x0F, 0x00, 0x00, 0x00, 0x70, 0x7F,
  0xFF, 0xC3, 0xE0, 0x00, 0x00, 0xE0, 0xFF, 0xFF, 0xF8, 0x78, 0x00, 0x00,
  0xE1, 0xFF, 0xFF, 0xFF, 0x1E, 0x00, 0x00, 0xE3, 0xFF, 0xFF, 0xFF, 0xE3,
  0x80, 0x00, 0xE3, 0xFF, 0xFF, 0xFF, 0xF8, 0xE0, 0x00, 0xE3, 0xFF, 0xFF,
  0xFF, 0xFE, 0x38, 0x00, 0x63, 0xFF, 0xFF, 0xFF, 0xFF, 0x8C, 0x00, 0x63,
  0xFF, 0xFF, 0xFF, 0xFF, 0xE7, 0x00, 0x63, 0xFF, 0xFF, 0xFF, 0xFF, 0xF9,
  0xC0, 0x31, 0xFF, 0xFF, 0xFF, 0xFF, 0xFE, 0x60, 0x31, 0xFF, 0xFF, 0xFF,
  0xFF, 0xFF, 0x38, 0x11, 0xFF, 0xFF, 0xFF, 0xFF, 0xFF, 0xCC, 0x18, 0xFF,
  0xFF, 0xC0, 0x7F, 0xFF, 0xE7, 0x08, 0xFF, 0xFF, 0x80, 0x0F, 0xFF, 0xF9,
  0x8C, 0x7F, 0xFF, 0x0F, 0xC1, 0xFF, 0xFC, 0xE6, 0x7F, 0xFF, 0x1F, 0xF8,
  0x7F, 0xFF, 0x32, 0x3F, 0xFF, 0x3C, 0x0F, 0x1F, 0xFF, 0x99, 0x1F, 0xFF,
  0xB8, 0x01, 0xCF, 0xFF, 0xCD, 0x8F, 0xFF, 0x98, 0x00, 0x63, 0xFF, 0xE7,
  0xCF, 0xFF, 0xD8, 0x00, 0x19, 0xFF, 0xFB, 0xE7, 0xFF, 0xCC, 0x00, 0x0C,
  0x7F, 0xFC, 0xF3, 0xFF, 0xEC, 0x00, 0x03, 0x3F, 0xFE, 0x79, 0xFF, 0xF6,
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
  {  2391,  36,  79,  41,    3,  -78 },   // 0x46 'F'
  {  2747,  58,  79,  62,    2,  -59 },   // 0x47 'G'
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

const GFXfont Neon64pt7b PROGMEM = {
  (uint8_t  *)Neon64pt7bBitmaps,
  (GFXglyph *)Neon64pt7bGlyphs,
  0x20, 0x7E, 105 };

// Approx. 24444 bytes
