pruttelherrie/Ehx9-All/controller-firmware/include/Amiga4Ever4pt7b.h

const uint8_t amiga4ever4pt7bBitmaps[] PROGMEM = {
  0x00, 0xFF, 0x0C, 0xDE, 0xC0, 0x6C, 0xDB, 0xFB, 0x6F, 0xED, 0x9B, 0x00,
  0x31, 0xFC, 0x1E, 0x0F, 0xE3, 0x00, 0x67, 0x5B, 0x61, 0xB6, 0xB9, 0x80,
  0x38, 0x6C, 0x68, 0x76, 0xDC, 0xCE, 0x7F, 0x6F, 0x00, 0x36, 0xCC, 0xC6,
  0x30, 0xC6, 0x33, 0x36, 0xC0, 0x66, 0x3C, 0xFF, 0x3C, 0x66, 0x30, 0xCF,
  0xCC, 0x30, 0x6F, 0x00, 0xFC, 0xF0, 0x03, 0x06, 0x0C, 0x18, 0x30, 0x60,
  0xC0, 0x7B, 0x3D, 0xFF, 0xEF, 0x37, 0x80, 0x37, 0xF3, 0x33, 0x30, 0x7B,
  0x30, 0xC6, 0x31, 0x8F, 0xC0, 0x7B, 0x30, 0xCE, 0x0F, 0x37, 0x80, 0x1C,
  0x79, 0xB6, 0x6F, 0xE1, 0x83, 0x00, 0xFF, 0x0F, 0x83, 0x0F, 0x37, 0x80,
  0x39, 0x8C, 0x3E, 0xCF, 0x37, 0x80, 0xFC, 0x30, 0xC6, 0x30, 0xC3, 0x00,
  0x7B, 0x3C, 0xDE, 0xCF, 0x37, 0x80, 0x7B, 0x3C, 0xDF, 0x0C, 0x67, 0x00,
  0xF0, 0xF0, 0x6C, 0x06, 0xF0, 0x0C, 0xCC, 0x0C, 0x0C, 0xFC, 0x0F, 0xC0,
  0xC0, 0xC0, 0xCC, 0xC0, 0x7B, 0x30, 0xC6, 0x30, 0x03, 0x00, 0x7D, 0x8F,
  0x7E, 0xBD, 0xF8, 0x1E, 0x00, 0x7B, 0x3C, 0xFF, 0xCF, 0x3C, 0xC0, 0xFB,
  0x3C, 0xFE, 0xCF, 0x3F, 0x80, 0x3D, 0x8C, 0x30, 0xC1, 0x83, 0xC0, 0xF3,
  0x6C, 0xF3, 0xCF, 0x6F, 0x00, 0xFF, 0x0C, 0x3C, 0xC3, 0x0F, 0xC0, 0xFF,
  0x0C, 0x3C, 0xC3, 0x0C, 0x00, 0x7B, 0x3C, 0x37, 0xCF, 0x37, 0xC0, 0xCF,
  0x3C, 0xFF, 0xCF, 0x3C, 0xC0, 0xF6, 0x66, 0x66, 0xF0, 0x0C, 0x30, 0xC3,
  0x0F, 0x37, 0x80, 0xC7, 0x9B, 0x67, 0x8D, 0x99, 0xB1, 0x80, 0xC3, 0x0C,
  0x30, 0xC3, 0x0F, 0xC0, 0xC7, 0xDF, 0xFE, 0xBC, 0x78, 0xF1, 0x80, 0xC7,
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
  {   179,   6,   7,   8,    1,   -6 },   // 0x46 'F'
  {   185,   6,   7,   8,    1,   -6 },   // 0x47 'G'
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

const GFXfont amiga4ever4pt7b PROGMEM = {
  (uint8_t  *)amiga4ever4pt7bBitmaps,
  (GFXglyph *)amiga4ever4pt7bGlyphs,
  0x20, 0x7E, 8 };

// Approx. 1141 bytes
