pruttelherrie/Ehx9-All/controller-firmware/include/digital7.h

const uint8_t digital_724pt7bBitmaps[] PROGMEM = {
  0x7F, 0xFE, 0xBF, 0xFF, 0xF3, 0xFF, 0xDF, 0x00, 0x07, 0xE0, 0x01, 0xF8,
  0x00, 0x7E, 0x00, 0x1F, 0x80, 0x07, 0xE0, 0x01, 0xF8, 0x00, 0x7E, 0x00,
  0x1F, 0x80, 0x07, 0xE0, 0x01, 0xF0, 0x00, 0x30, 0x00, 0x00, 0x00, 0x00,
  0x00, 0x00, 0x30, 0x00, 0x3E, 0x00, 0x1F, 0x80, 0x07, 0xE0, 0x01, 0xF8,
  0x00, 0x7E, 0x00, 0x1F, 0x80, 0x07, 0xE0, 0x01, 0xF8, 0x00, 0x7E, 0x00,
  0x1F, 0x00, 0x07, 0x7F, 0xFD, 0xFF, 0xFF, 0xF7, 0xFF, 0xE8, 0x4F, 0xFF,
  0xFF, 0xFF, 0xFE, 0xC8, 0x2F, 0xFF, 0xFF, 0xFF, 0xFE, 0xD0, 0x7F, 0xFE,
  0xBF, 0xFF, 0xF3, 0xFF, 0xDC, 0x00, 0x07, 0x00, 0x01, 0xC0, 0x00, 0x70,
  0x00, 0x1C, 0x00, 0x07, 0x00, 0x01, 0xC0, 0x00, 0x70, 0x00, 0x1C, 0x00,
  0x07, 0x00, 0x01, 0xC0, 0x00, 0x33, 0xFF, 0xF1, 0xFF, 0xFE, 0x3F, 0xFF,
  0x30, 0x00, 0x0E, 0x00, 0x03, 0x80, 0x00, 0xE0, 0x00, 0x38, 0x00, 0x0E,
  0x00, 0x03, 0x80, 0x00, 0xE0, 0x00, 0x38, 0x00, 0x0E, 0x00, 0x03, 0x00,
  0x00, 0x7F, 0xFE, 0x3F, 0xFF, 0xC7, 0xFF, 0xF0, 0x7F, 0xFE, 0x9F, 0xFF,
  0xF3, 0xFF, 0xDC, 0x00, 0x07, 0x00, 0x01, 0xC0, 0x00, 0x70, 0x00, 0x1C,
  0x00, 0x07, 0x00, 0x01, 0xC0, 0x00, 0x70, 0x00, 0x1C, 0x00, 0x07, 0x00,
  0x01, 0xC0, 0x00, 0x31, 0xFF, 0xF0, 0xFF, 0xFE, 0x1F, 0xFF, 0x00, 0x00,
  0x30, 0x00, 0x1C, 0x00, 0x07, 0x00, 0x01, 0xC0, 0x00, 0x70, 0x00, 0x1C,
  0x00, 0x07, 0x00, 0x01, 0xC0, 0x00, 0x70, 0x00, 0x1C, 0x00, 0x07, 0x3F,
  0xFD, 0xDF, 0xFF, 0xF7, 0xFF, 0xE8, 0x00, 0x00, 0x80, 0x00, 0x3C, 0x00,
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
  {  1013,  16,  31,  21,    2,  -30 },   // 0x43 'C'
  {  1075,  18,  31,  22,    2,  -30 } }; // 0x44 'D'

const GFXfont digital_724pt7b PROGMEM = {
  (uint8_t  *)digital_724pt7bBitmaps,
  (GFXglyph *)digital_724pt7bGlyphs,
  0x30, 0x44, 26 };

// Approx. 1299 bytes
