pruttelherrie/Ehx9-All/controller-firmware/include/neon8.h

#ifndef __NEON8__

#define __NEON8__

const uint8_t Neon8pt7bBitmaps[] PROGMEM = {
  0x00, 0x00, 0x00, 0x00, 0x00, 0x00, 0x00, 0x00, 0x00, 0x00, 0x00, 0x00,
  0x00, 0x00, 0x00, 0x00, 0x00, 0x00, 0x00, 0x00, 0x00, 0x00, 0x00, 0x00,
  0x00, 0x00, 0x00, 0x00, 0x00, 0x00, 0x00, 0x00, 0x00, 0x3D, 0xFF, 0x1E,
  0x3C, 0x7F, 0xCF, 0x80, 0xC1, 0x83, 0x07, 0xEF, 0xF8, 0xF1, 0xE3, 0xFE,
  0xF8, 0x7D, 0xFF, 0x2E, 0x6F, 0xFF, 0xDF, 0x00, 0x06, 0x0C, 0x19, 0xF7,
  0xFF, 0xF1, 0xE3, 0xC7, 0xFD, 0xF0, 0x3C, 0xFF, 0xBE, 0xEF, 0xF7, 0xDF,
  0x00, 0x3B, 0xF9, 0xCF, 0xFF, 0x9C, 0xE7, 0x00, 0x7E, 0xBF, 0xE3, 0xE3,
  0x7F, 0x7F, 0x23, 0x3F, 0x3E, 0xC1, 0x83, 0xE7, 0xEE, 0xF8, 0xF1, 0xE3,
  0xC7, 0x8C, 0xFF, 0xFC, 0x18, 0xC6, 0x31, 0x8C, 0x67, 0xF7, 0x80, 0xC1,
  0x83, 0x1E, 0x3C, 0xFF, 0xFF, 0xE3, 0xC7, 0x9C, 0xFF, 0xFF, 0xFF, 0xFC,
  0x7F, 0xEF, 0xFF, 0xC6, 0x3C, 0x63, 0xC6, 0x3C, 0x63, 0xC6, 0x30, 0x3E,
  0x7F, 0xE7, 0xE3, 0xE3, 0xE3, 0xE3, 0x3C, 0xFF, 0xF3, 0xE3, 0xF3, 0xFF,
  0x3C, 0x3C, 0x7E, 0xFF, 0xE3, 0xE3, 0xE3, 0xFE, 0xFC, 0xE0, 0xE0, 0xC0,
  0x38, 0xFB, 0xFE, 0x3C, 0x78, 0xDF, 0x9F, 0x06, 0x0C, 0x18, 0x7B, 0xF9,
  0xCE, 0x73, 0x80, 0xFF, 0xFF, 0x0F, 0xFF, 0xFF, 0xFF, 0x00, 0xE7, 0x39,
  0xCF, 0xFF, 0x9B, 0x7B, 0xC0, 0xE3, 0xE3, 0xE3, 0xE3, 0xDF, 0x7E, 0x3C,
  0xE3, 0xBF, 0x8D, 0x8B, 0xC3, 0xC1, 0x60, 0x60, 0x10, 0xC6, 0x3C, 0x63,
  0xC6, 0x3C, 0x63, 0xFF, 0xF7, 0x9E, 0x7F, 0xC0, 0xFF, 0xFF, 0x18, 0x18,
  0xFF, 0xE7, 0xFF, 0xC3, 0xE3, 0xE3, 0xE3, 0xE3, 0xDF, 0x7F, 0x23, 0x3F,
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
  {    73,   5,  10,   6,    0,   -9 },   // 0x46 'F'
  {    80,   8,   9,   8,   -1,   -6 },   // 0x47 'G'
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

const GFXfont Neon8pt7b PROGMEM = {
  (uint8_t  *)Neon8pt7bBitmaps,
  (GFXglyph *)Neon8pt7bGlyphs,
  0x20, 0x7E, 13 };

// Approx. 1117 bytes
#endif
