pruttelherrie/Ehx9-All/controller-firmware/src/tcMenuTfteSpi.cpp

/*
 * Copyright (c) 2018 https://www.thecoderscorner.com (Nutricherry LTD).
 * This product is licensed under an Apache license, see the LICENSE file in the top-level directory.
 */

/**
 * TFT_eSPI renderer that renders menus onto this type of display. This file is a plugin file and should not
 * be directly edited, it will be replaced each time the project is built. If you want to edit this file in place,
 * make sure to rename it first.
 *
 * LIBRARY REQUIREMENT
 * This library requires the AdaGfx library along with a suitable driver.
 */


#include "tcMenuTfteSpi.h"
#include <TFT_eSPI.h>

TfteSpiDrawable::TfteSpiDrawable(TFT_eSPI *tft, int spriteHeight) : tft(tft), spriteWithConfig(nullptr), spriteHeight(spriteHeight) {}

DeviceDrawable *TfteSpiDrawable::getSubDeviceFor(const Coord &where, const Coord& size, const color_t *palette, int paletteSize) {
    if(paletteSize > SPRITE_PALETTE_SIZE) return nullptr; // cant exceed color palette size

    if(spriteWithConfig == nullptr) spriteWithConfig = new TftSpriteAndConfig(this, tft->width(), spriteHeight);
    if(!spriteWithConfig) return nullptr;

    if(spriteWithConfig->initSprite(where, size, palette, paletteSize)) {
        return spriteWithConfig;
    }
    else return nullptr;
}

void TfteSpiDrawable::drawText(const Coord &where, const void *font, int mag, const char *text) {
    fontPtrToNum(font, mag);
    tft->setTextColor(drawColor, drawColor); // transparent background
    tft->drawString(text, where.x, where.y);
}

void TfteSpiDrawable::drawBitmap(const Coord &where, const DrawableIcon *icon, bool selected) {
    if(icon->getIconType() == DrawableIcon::ICON_XBITMAP) {
        tft->drawXBitmap(where.x, where.y, icon->getIcon(selected), icon->getDimensions().x, icon->getDimensions().y, drawColor, backgroundColor);
    }
    else if(icon->getIconType() == DrawableIcon::ICON_MONO) {
        tft->drawBitmap(where.x, where.y, icon->getIcon(selected), icon->getDimensions().x, icon->getDimensions().y, drawColor, backgroundColor);
    }
    else if(icon->getIconType() == DrawableIcon::ICON_NATIVE) {
        tft->pushImage(where.x, where.y, icon->getDimensions().x, icon->getDimensions().y, (const uint16_t*)icon->getIcon(selected));
    }
}

void TfteSpiDrawable::drawXBitmap(const Coord &where, const Coord &size, const uint8_t *data) {
    tft->drawXBitmap(where.x, where.y, data, size.x, size.y, drawColor, backgroundColor);
}

void TfteSpiDrawable::drawBox(const Coord &where, const Coord &size, bool filled) {
    if(filled) {
        tft->fillRect(where.x, where.y, size.x, size.y, drawColor);
    }
    else {
        tft->drawRect(where.x, where.y, size.x, size.y, drawColor);
    }
}

void TfteSpiDrawable::drawCircle(const Coord &where, int radius, bool filled) {
    if(filled) {
        tft->fillCircle(where.x, where.y, radius, drawColor);
    }
    else {
        tft->drawCircle(where.x, where.y, radius, drawColor);
    }
}

void TfteSpiDrawable::drawPolygon(const Coord *points, int numPoints, bool filled) {
    if(numPoints == 2) {
        tft->drawLine(points[0].x, points[0].y, points[1].x, points[1].y, drawColor);
    }
    else if(numPoints == 3) {
        if(filled) {
            tft->fillTriangle(points[0].x, points[0].y, points[1].x, points[1].y, points[2].x, points[2].y, drawColor);
        }
        else {
            tft->drawTriangle(points[0].x, points[0].y, points[1].x, points[1].y, points[2].x, points[2].y, drawColor);
        }
    }
}

void TfteSpiDrawable::transaction(bool isStarting, bool redrawNeeded) {
    if(isStarting) tft->setTextDatum(TL_DATUM);
}

Coord TfteSpiDrawable::textExtents(const void *font, int mag, const char *text, int *baseline) {
    if(baseline) *baseline = 0;
    fontPtrToNum(font, mag);
    return Coord(tft->textWidth(text), tft->fontHeight());
}

void TfteSpiDrawable::fontPtrToNum(const void* font, int mag) {
#ifdef LOAD_GFXFF
    if(font == nullptr) {
        tft->setTextFont((uint8_t) mag); //    <= does not work, for some reason GLCD data structure is not found
    }
    else {
        tft->setFreeFont(static_cast<const GFXfont *>(font)); 
    }
#else
    tft->setTextFont((uint8_t) mag); // numbered font does not take font data, just a number
#endif
}

//
// Sprite object
//

TftSpriteAndConfig::TftSpriteAndConfig(TfteSpiDrawable *root, int width, int height) : TfteSpiDrawable(&sprite, 0),
        root(root), sprite(root->getTFT()), where(0,0), currentSize(0, 0), size(width, height), currentColorsDefined(0) {
}

bool TftSpriteAndConfig::initSprite(const Coord &spriteWhere, const Coord &spriteSize, const color_t* palette, int palEntries) {
    // if the area is too big, or the sprite is in use, don't proceed.
    if(spriteSize.x > size.x || spriteSize.y > size.y) return false;

    // create the sprite if needed
    if(!sprite.created()) {
        sprite.createSprite(size.x, size.y);
        sprite.setColorDepth(4);
    }
    for(int i=0; i<palEntries;i++) {
        sprite.setPaletteColor(i, palette[i]);
        currentColorsDefined = palEntries;
    }

    // set the positions and return.
    where = spriteWhere;
    currentSize = spriteSize;

    return sprite.created();
}

color_t TftSpriteAndConfig::getUnderlyingColor(color_t theColor) {
    for(int i=0;i<currentColorsDefined;i++) {
        if(sprite.getPaletteColor(i) == theColor) return i;
    }

    if(currentColorsDefined < SPRITE_PALETTE_SIZE) {
        sprite.setPaletteColor(currentColorsDefined, theColor);
        return currentColorsDefined++;
    }

    return 0;
}

void TftSpriteAndConfig::transaction(bool isStarting, bool redrawNeeded) {
    if(!isStarting) {
        // if it's ending, we push the sprite.
        sprite.pushSprite(where.x, where.y, 0, 0, currentSize.x, currentSize.y);
    }
}
